Ttl/detector/ad8319cal.py

#900 Mhz
cal_table = \
{900:
[
(-60.14493815849747, 1.5322033898305083),
(-56.35923041685753, 1.511864406779661),
(-51.625011452130096, 1.464406779661017),
(-47.07805771873568, 1.3966101694915256),
(-6.126614750343563, 0.4813559322033898),
(-1.5790196976637816, 0.40677966101694896),
(2.9653687585891078, 0.36610169491525424),
(5.994319743472289, 0.34576271186440666),
(7.507833256985805, 0.345)
],

#3.6 Ghz
3600:
[
(-60.046174988547875, 1.511864406779661),
(-56.264956481905614, 1.4847457627118643),
(-51.35309207512597, 1.4101694915254237),
(-45.878790655061835, 1.2813559322033898),
(-9.632707283554737, 0.45423728813559316),
(-4.910673385249652, 0.3728813559322033),
(-1.5078332569858048, 0.34576271186440666),
(2.653046266605571, 0.33220338983050857)
],

#1.9 GHz
1900:
[
(-59.81029810298102, 1.5186440677966102),
(-55.44715447154471, 1.4847457627118645),
(-51.46341463414633, 1.4372881355932199),
(-46.5311653116531, 1.3355932203389829),
(-6.314363143631411, 0.4474576271186441),
(-2.520325203252014, 0.38644067796610226),
(0.8943089430894418, 0.3525423728813557),
(5.257452574525757, 0.3389830508474576)
],

#5.8 GHz
5800:
[
(-59.81029810298102, 1.5322217628955954),
(-56.01626016260161, 1.519029902163429),
(-51.84281842818427, 1.4855358045105875),
(-48.617886178861795, 1.4316108584814664),
(-40.08130081300814, 1.256166459969685),
(-3.6585365853658516, 0.4461347664324107),
(-0.8130081300813004, 0.3921730742731162),
(2.2222222222222285, 0.3721280602636545),
(4.498644986449847, 0.36556887602774424)
],

#2.2 GHz
2200:
[
(-59.811320754716974, 1.5151515151515151),
(-55.66037735849055, 1.4882154882154883),
(-52.26415094339622, 1.447811447811448),
(-48.67924528301886, 1.3737373737373737),
(-7.358490566037716, 0.46464646464646453),
(-3.5849056603773306, 0.404040404040404),
(0.1886792452830548, 0.3636363636363633),
(3.9622641509434118, 0.343434343434343)
],

#8.0 GHz
8000:
[
(-60.18970189701898, 1.5322033898305083),
(-57.15447154471545, 1.5254237288135593),
(-52.03252032520328, 1.5118644067796607),
(-46.91056910569105, 1.457627118644068),
(-41.40921409214093, 1.376271186440678),
(-9.72899728997291, 0.6711864406779662),
(-4.6070460704607115, 0.5423728813559325),
(-1.382113821138205, 0.4745762711864412),
(1.653116531165324, 0.46101694915254265),
(5.826558265582662, 0.42033898305084794),
(10.189701897018978, 0.33898305084745806)
]
}
