Ttl/detector/detector/example/src/cdc_main.c

/*
 * @brief Vitual communication port example
 *
 * @note
 * Copyright(C) NXP Semiconductors, 2013
 * All rights reserved.
 *
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
 * @par
 * Permission to use, copy, modify, and distribute this software and its
 * documentation is hereby granted, under NXP Semiconductors' and its
 * licensor's relevant copyrights in the software, without fee, provided that it
 * is used in conjunction with NXP Semiconductors microcontrollers.  This
 * copyright, permission, and disclaimer notice must appear in all copies of
 * this code.
 */

#include "board.h"
#include <stdio.h>
#include <string.h>
#include "app_usbd_cfg.h"
#include "cdc_vcom.h"

#define TICKRATE_HZ (100)	/* 100 ticks per second */
#define ADC_SAMPLE_COUNTER 2 /* Tick to trigger ADC */

#define BOARD_ADC_CH 1

static volatile int ticks;
static bool sequenceComplete, thresholdCrossed;

static USBD_HANDLE_T g_hUsb;
static uint8_t g_rxBuff[256];

const  USBD_API_T *g_pUsbApi;

/*****************************************************************************
 * Private functions
 ****************************************************************************/

/*****************************************************************************
 * Public functions
 ****************************************************************************/

/**
 * @brief	Handle interrupt from SysTick timer
 * @return	Nothing
 */
void SysTick_Handler(void)
{
	static uint32_t count;

	count++;
	if (count >= ADC_SAMPLE_COUNTER) {
		count = 0;

		/* Manual start for ADC conversion sequence A */
		Chip_ADC_StartSequencer(LPC_ADC, ADC_SEQA_IDX);
	}
}

/**
 * @brief	Handle interrupt from ADC sequencer A
 * @return	Nothing
 */
void ADCA_IRQHandler(void)
{
	uint32_t pending;

	/* Get pending interrupts */
	pending = Chip_ADC_GetFlags(LPC_ADC);

	/* Sequence A completion interrupt */
	if (pending & ADC_FLAGS_SEQA_INT_MASK) {
		sequenceComplete = true;
	}

	/* Threshold crossing interrupt on ADC input channel */
	if (pending & ADC_FLAGS_THCMP_MASK(BOARD_ADC_CH)) {
		thresholdCrossed = true;
	}

	/* Clear any pending interrupts */
	Chip_ADC_ClearFlags(LPC_ADC, pending);
}

/**
 * @brief	Handle interrupt from USB0
 * @return	Nothing
 */
void USB_IRQHandler(void)
{
	uint32_t *addr = (uint32_t *) LPC_USB->EPLISTSTART;

	/*	WORKAROUND for artf32289 ROM driver BUG:
	    As part of USB specification the device should respond
	    with STALL condition for any unsupported setup packet. The host will send
	    new setup packet/request on seeing STALL condition for EP0 instead of sending
	    a clear STALL request. Current driver in ROM doesn't clear the STALL
	    condition on new setup packet which should be fixed.
	 */
	if ( LPC_USB->DEVCMDSTAT & _BIT(8) ) {	/* if setup packet is received */
		addr[0] &= ~(_BIT(29));	/* clear EP0_OUT stall */
		addr[2] &= ~(_BIT(29));	/* clear EP0_IN stall */
	}
	USBD_API->hw->ISR(g_hUsb);
}

/* Find the address of interface descriptor for given class type. */
USB_INTERFACE_DESCRIPTOR *find_IntfDesc(const uint8_t *pDesc, uint32_t intfClass)
{
	USB_COMMON_DESCRIPTOR *pD;
	USB_INTERFACE_DESCRIPTOR *pIntfDesc = 0;
	uint32_t next_desc_adr;

	pD = (USB_COMMON_DESCRIPTOR *) pDesc;
	next_desc_adr = (uint32_t) pDesc;

	while (pD->bLength) {
		/* is it interface descriptor */
		if (pD->bDescriptorType == USB_INTERFACE_DESCRIPTOR_TYPE) {

			pIntfDesc = (USB_INTERFACE_DESCRIPTOR *) pD;
			/* did we find the right interface descriptor */
			if (pIntfDesc->bInterfaceClass == intfClass) {
				break;
			}
		}
		pIntfDesc = 0;
		next_desc_adr = (uint32_t) pD + pD->bLength;
		pD = (USB_COMMON_DESCRIPTOR *) next_desc_adr;
	}

	return pIntfDesc;
}

/**
 * @brief	main routine for blinky example
 * @return	Function should not exit.
 */
int main(void)
{
	uint32_t rawSample;
	USBD_API_INIT_PARAM_T usb_param;
	USB_CORE_DESCS_T desc;
	ErrorCode_t ret = LPC_OK;
	uint32_t rdCnt = 0;

	SystemCoreClockUpdate();
	/* Initialize board and chip */
	Board_Init();

	/* Configure T_ADJ(PIO0_16) pin as output */
	Chip_GPIO_SetPinDIROutput(LPC_GPIO, 0, 16);
	Chip_GPIO_SetPinState(LPC_GPIO, 0, 16, false);

	/* Setup ADC for 12-bit mode and normal power */
	Chip_ADC_Init(LPC_ADC, 0);

	/* Need to do a calibration after initialization and trim */
	Chip_ADC_StartCalibration(LPC_ADC);
	while (!(Chip_ADC_IsCalibrationDone(LPC_ADC))) {}

	/* Setup ADC clock rate using sycnchronous clocking */
	Chip_ADC_SetClockRate(LPC_ADC, 1000000);

	/* Setup a sequencer to do the following:
	   Perform ADC conversion of ADC channels 1 only */
	Chip_ADC_SetupSequencer(LPC_ADC, ADC_SEQA_IDX,
		(ADC_SEQ_CTRL_CHANSEL(BOARD_ADC_CH) | ADC_SEQ_CTRL_MODE_EOS));

	/* ADC input 1 is on PIO0_23 mapped to FUNC2 */
	Chip_IOCON_PinMuxSet(LPC_IOCON, 0, 23, (IOCON_FUNC1 | IOCON_MODE_INACT |
										   IOCON_ADMODE_EN));
	/* Use higher voltage trim */
	Chip_ADC_SetTrim(LPC_ADC, ADC_TRIM_VRANGE_HIGHV);

	/* Clear all pending interrupts */
	Chip_ADC_ClearFlags(LPC_ADC, Chip_ADC_GetFlags(LPC_ADC));

	/* Enable ADC overrun and sequence A completion interrupts */
	Chip_ADC_EnableInt(LPC_ADC, (ADC_INTEN_SEQA_ENABLE | ADC_INTEN_OVRRUN_ENABLE));

	/* Enable ADC NVIC interrupt */
	NVIC_EnableIRQ(ADC_A_IRQn);

	/* Enable sequencer */
	Chip_ADC_EnableSequencer(LPC_ADC, ADC_SEQA_IDX);

	/* This example uses the periodic sysTick to manually trigger the ADC,
	   but a periodic timer can be used in a match configuration to start
	   an ADC sequence without software intervention. */
	SysTick_Config(SystemCoreClock / TICKRATE_HZ);

	/* enable clocks and pinmux */
	Chip_USB_Init();

	/* initialize USBD ROM API pointer. */
	g_pUsbApi = (const USBD_API_T *) LPC_ROM_API->usbdApiBase;

	/* initialize call back structures */
	memset((void *) &usb_param, 0, sizeof(USBD_API_INIT_PARAM_T));
	usb_param.usb_reg_base = LPC_USB0_BASE;
	/*	WORKAROUND for artf44835 ROM driver BUG:
	    Code clearing STALL bits in endpoint reset routine corrupts memory area
	    next to the endpoint control data. For example When EP0, EP1_IN, EP1_OUT,
	    EP2_IN are used we need to specify 3 here. But as a workaround for this
	    issue specify 4. So that extra EPs control structure acts as padding buffer
	    to avoid data corruption. Corruption of padding memory doesn’t affect the
	    stack/program behaviour.
	 */
	usb_param.max_num_ep = 3 + 1;
	usb_param.mem_base = USB_STACK_MEM_BASE;
	usb_param.mem_size = USB_STACK_MEM_SIZE;

	/* Set the USB descriptors */
	desc.device_desc = (uint8_t *) &USB_DeviceDescriptor[0];
	desc.string_desc = (uint8_t *) &USB_StringDescriptor[0];
	/* Note, to pass USBCV test full-speed only devices should have both
	   descriptor arrays point to same location and device_qualifier set to 0.
	 */
	desc.high_speed_desc = (uint8_t *) &USB_FsConfigDescriptor[0];
	desc.full_speed_desc = (uint8_t *) &USB_FsConfigDescriptor[0];
	desc.device_qualifier = 0;

	/* USB Initialization */
	ret = USBD_API->hw->Init(&g_hUsb, &desc, &usb_param);
	if (ret == LPC_OK) {

		/*	WORKAROUND for artf32219 ROM driver BUG:
		    The mem_base parameter part of USB_param structure returned
		    by Init() routine is not accurate causing memory allocation issues for
		    further components.
		 */
		usb_param.mem_base = USB_STACK_MEM_BASE + (USB_STACK_MEM_SIZE - usb_param.mem_size);

		/* Init VCOM interface */
		ret = vcom_init(g_hUsb, &desc, &usb_param);
		if (ret == LPC_OK) {
			/*  enable USB interrupts */
			NVIC_EnableIRQ(USB0_IRQn);
			/* now connect */
			USBD_API->hw->Connect(g_hUsb, 1);
		}

	}

	while (1) {
		if (vcom_connected()) {
			if ((rdCnt = vcom_bread(&g_rxBuff[0], 256))) {
				//Set TADJ pin high/low
				if (g_rxBuff[0] == 0xF0) {
					Chip_GPIO_SetPinState(LPC_GPIO, 0, 16, false);
				} else if (g_rxBuff[0] == 0xF1) {
					Chip_GPIO_SetPinState(LPC_GPIO, 0, 16, true);
				} else if (g_rxBuff[0] == 0xF2) {
					Board_LED_Set(0, false);
				} else if (g_rxBuff[0] == 0xF3) {
					Board_LED_Set(0, true);
				}

			}
			/* Is a conversion sequence complete? */
			if (sequenceComplete) {
				sequenceComplete = false;

				rawSample = ADC_DR_RESULT(Chip_ADC_GetDataReg(LPC_ADC, 1));
				vcom_write((uint8_t*)&rawSample, 2);
			}
		}

		/* Sleep until next IRQ happens */
		__WFI();
	}
}
