Ttl/detector/detector/example/src/cdc_vcom.c

/*
 * @brief Virtual Comm port call back routines
 *
 * @note
 * Copyright(C) NXP Semiconductors, 2013
 * All rights reserved.
 *
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
 * @par
 * Permission to use, copy, modify, and distribute this software and its
 * documentation is hereby granted, under NXP Semiconductors' and its
 * licensor's relevant copyrights in the software, without fee, provided that it
 * is used in conjunction with NXP Semiconductors microcontrollers.  This
 * copyright, permission, and disclaimer notice must appear in all copies of
 * this code.
 */
#include <string.h>
#include "app_usbd_cfg.h"
#include "board.h"
#include "cdc_vcom.h"

/*****************************************************************************
 * Private types/enumerations/variables
 ****************************************************************************/

/*****************************************************************************
 * Public types/enumerations/variables
 ****************************************************************************/

/**
 * Global variable to hold Virtual COM port control data.
 */
VCOM_DATA_T g_vCOM;

/*****************************************************************************
 * Private functions
 ****************************************************************************/

/* VCOM bulk EP_IN endpoint handler */
static ErrorCode_t VCOM_bulk_in_hdlr(USBD_HANDLE_T hUsb, void *data, uint32_t event)
{
	VCOM_DATA_T *pVcom = (VCOM_DATA_T *) data;

	if (event == USB_EVT_IN) {
		pVcom->tx_flags &= ~VCOM_TX_BUSY;
	}
	return LPC_OK;
}

/* VCOM bulk EP_OUT endpoint handler */
static ErrorCode_t VCOM_bulk_out_hdlr(USBD_HANDLE_T hUsb, void *data, uint32_t event)
{
	VCOM_DATA_T *pVcom = (VCOM_DATA_T *) data;

	switch (event) {
	case USB_EVT_OUT:
		pVcom->rx_count = USBD_API->hw->ReadEP(hUsb, USB_CDC_OUT_EP, pVcom->rx_buff);
		if (pVcom->rx_flags & VCOM_RX_BUF_QUEUED) {
			pVcom->rx_flags &= ~VCOM_RX_BUF_QUEUED;
			if (pVcom->rx_count != 0) {
				pVcom->rx_flags |= VCOM_RX_BUF_FULL;
			}

		}
		else if (pVcom->rx_flags & VCOM_RX_DB_QUEUED) {
			pVcom->rx_flags &= ~VCOM_RX_DB_QUEUED;
			pVcom->rx_flags |= VCOM_RX_DONE;
		}
		break;

	case USB_EVT_OUT_NAK:
		/* queue free buffer for RX */
		if ((pVcom->rx_flags & (VCOM_RX_BUF_FULL | VCOM_RX_BUF_QUEUED)) == 0) {
			USBD_API->hw->ReadReqEP(hUsb, USB_CDC_OUT_EP, pVcom->rx_buff, VCOM_RX_BUF_SZ);
			pVcom->rx_flags |= VCOM_RX_BUF_QUEUED;
		}
		break;

	default:
		break;
	}

	return LPC_OK;
}

/* Set line coding call back routine */
static ErrorCode_t VCOM_SetLineCode(USBD_HANDLE_T hCDC, CDC_LINE_CODING *line_coding)
{
	VCOM_DATA_T *pVcom = &g_vCOM;

	/* Called when baud rate is changed/set. Using it to know host connection state */
	pVcom->tx_flags = VCOM_TX_CONNECTED;	/* reset other flags */

	return LPC_OK;
}

/*****************************************************************************
 * Public functions
 ****************************************************************************/

/* Virtual com port init routine */
ErrorCode_t vcom_init(USBD_HANDLE_T hUsb, USB_CORE_DESCS_T *pDesc, USBD_API_INIT_PARAM_T *pUsbParam)
{
	USBD_CDC_INIT_PARAM_T cdc_param;
	ErrorCode_t ret = LPC_OK;
	uint32_t ep_indx;

	g_vCOM.hUsb = hUsb;
	memset((void *) &cdc_param, 0, sizeof(USBD_CDC_INIT_PARAM_T));
	cdc_param.mem_base = pUsbParam->mem_base;
	cdc_param.mem_size = pUsbParam->mem_size;
	cdc_param.cif_intf_desc = (uint8_t *) find_IntfDesc(pDesc->high_speed_desc, CDC_COMMUNICATION_INTERFACE_CLASS);
	cdc_param.dif_intf_desc = (uint8_t *) find_IntfDesc(pDesc->high_speed_desc, CDC_DATA_INTERFACE_CLASS);
	cdc_param.SetLineCode = VCOM_SetLineCode;

	ret = USBD_API->cdc->init(hUsb, &cdc_param, &g_vCOM.hCdc);

	if (ret == LPC_OK) {
		/* allocate transfer buffers */
		g_vCOM.rx_buff = (uint8_t *) cdc_param.mem_base;
		cdc_param.mem_base += VCOM_RX_BUF_SZ;
		cdc_param.mem_size -= VCOM_RX_BUF_SZ;

		/* register endpoint interrupt handler */
		ep_indx = (((USB_CDC_IN_EP & 0x0F) << 1) + 1);
		ret = USBD_API->core->RegisterEpHandler(hUsb, ep_indx, VCOM_bulk_in_hdlr, &g_vCOM);
		if (ret == LPC_OK) {
			/* register endpoint interrupt handler */
			ep_indx = ((USB_CDC_OUT_EP & 0x0F) << 1);
			ret = USBD_API->core->RegisterEpHandler(hUsb, ep_indx, VCOM_bulk_out_hdlr, &g_vCOM);

		}
		/* update mem_base and size variables for cascading calls. */
		pUsbParam->mem_base = cdc_param.mem_base;
		pUsbParam->mem_size = cdc_param.mem_size;
	}

	return ret;
}

/* Virtual com port buffered read routine */
uint32_t vcom_bread(uint8_t *pBuf, uint32_t buf_len)
{
	VCOM_DATA_T *pVcom = &g_vCOM;
	uint16_t cnt = 0;
	/* read from the default buffer if any data present */
	if (pVcom->rx_count) {
		cnt = (pVcom->rx_count < buf_len) ? pVcom->rx_count : buf_len;
		memcpy(pBuf, pVcom->rx_buff, cnt);
		pVcom->rx_rd_count += cnt;

		/* enter critical section */
		NVIC_DisableIRQ(USB0_IRQn);
		if (pVcom->rx_rd_count >= pVcom->rx_count) {
			pVcom->rx_flags &= ~VCOM_RX_BUF_FULL;
			pVcom->rx_rd_count = pVcom->rx_count = 0;
		}
		/* exit critical section */
		NVIC_EnableIRQ(USB0_IRQn);
	}
	return cnt;
}

/* Virtual com port read routine */
ErrorCode_t vcom_read_req(uint8_t *pBuf, uint32_t len)
{
	VCOM_DATA_T *pVcom = &g_vCOM;

	/* check if we queued Rx buffer */
	if (pVcom->rx_flags & (VCOM_RX_BUF_QUEUED | VCOM_RX_DB_QUEUED)) {
		return ERR_BUSY;
	}
	/* enter critical section */
	NVIC_DisableIRQ(USB0_IRQn);
	/* if not queue the request and return 0 bytes */
	USBD_API->hw->ReadReqEP(pVcom->hUsb, USB_CDC_OUT_EP, pBuf, len);
	/* exit critical section */
	NVIC_EnableIRQ(USB0_IRQn);
	pVcom->rx_flags |= VCOM_RX_DB_QUEUED;

	return LPC_OK;
}

/* Gets current read count. */
uint32_t vcom_read_cnt(void)
{
	VCOM_DATA_T *pVcom = &g_vCOM;
	uint32_t ret = 0;

	if (pVcom->rx_flags & VCOM_RX_DONE) {
		ret = pVcom->rx_count;
		pVcom->rx_count = 0;
	}

	return ret;
}

/* Virtual com port write routine*/
uint32_t vcom_write(uint8_t *pBuf, uint32_t len)
{
	VCOM_DATA_T *pVcom = &g_vCOM;
	uint32_t ret = 0;

	if ( (pVcom->tx_flags & VCOM_TX_CONNECTED) && ((pVcom->tx_flags & VCOM_TX_BUSY) == 0) ) {
		pVcom->tx_flags |= VCOM_TX_BUSY;

		/* enter critical section */
		NVIC_DisableIRQ(USB0_IRQn);
		ret = USBD_API->hw->WriteEP(pVcom->hUsb, USB_CDC_IN_EP, pBuf, len);
		/* exit critical section */
		NVIC_EnableIRQ(USB0_IRQn);
	}

	return ret;
}
